thorsten-l/ESP8266-WiFi-Doorbell-Gateway/kicad/wifidoorbell/WifiDoorBell-D1-mini-B.Cu.pdf

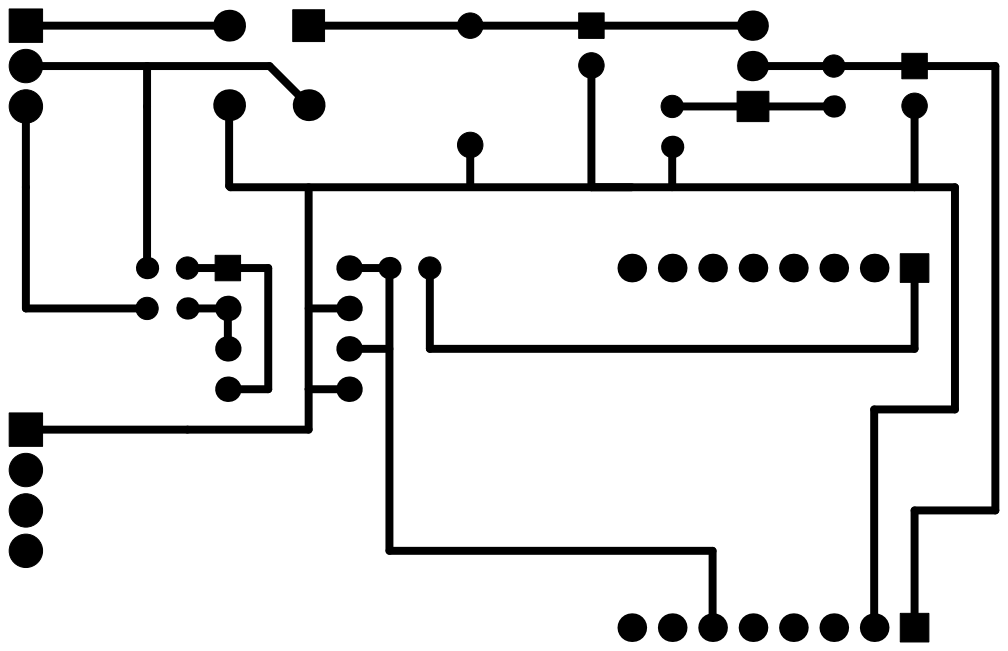
[picture p16: page 1]
