thorsten-l/ESP8266-WiFi-Doorbell-Gateway/kicad/wifidoorbell/WifiDoorBell-D1-mini-B.Mask.pdf

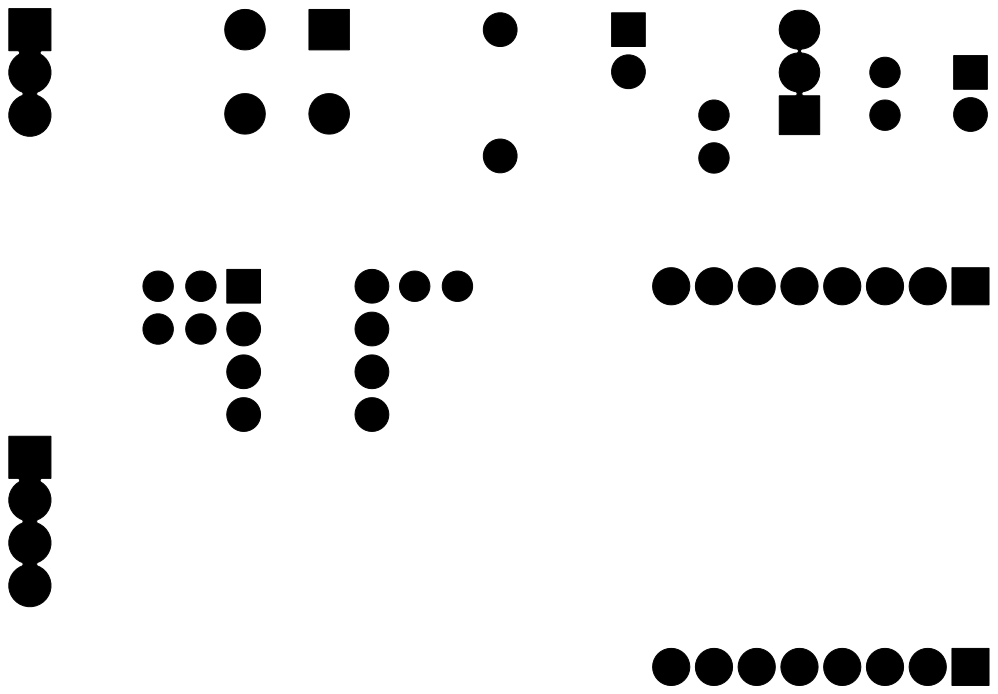
[picture p17: page 1]
