thorsten-l/ESP8266-WiFi-Doorbell-Gateway/kicad/wifidoorbell/WifiDoorBell-D1-mini-F.CrtYd.pdf

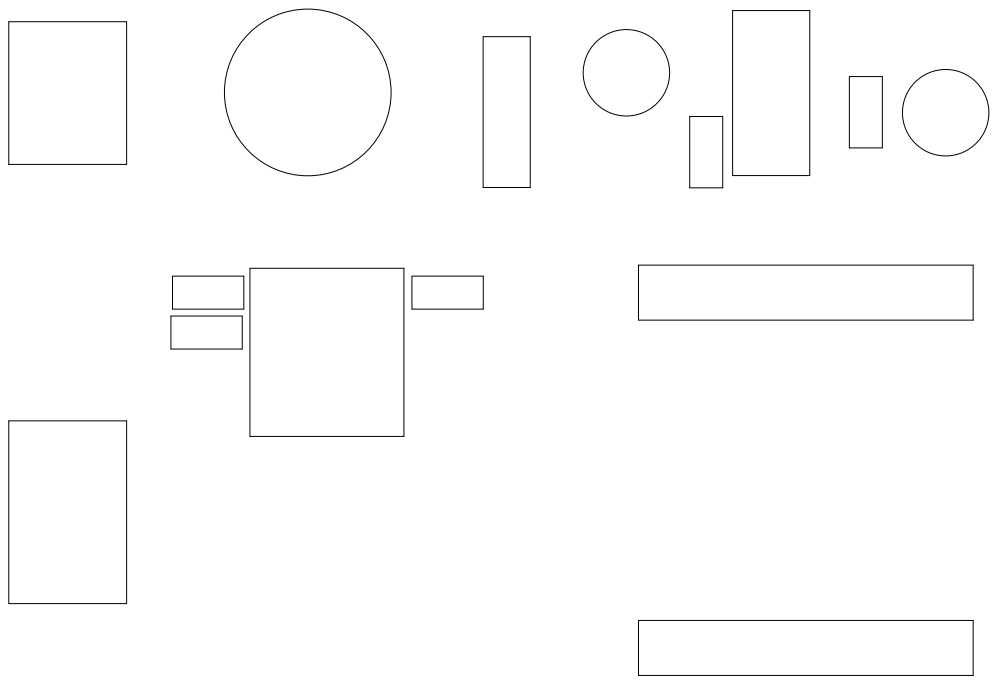
[picture p18: page 1]
