thorsten-l/ESP8266-WiFi-Doorbell-Gateway/kicad/wifidoorbell/WifiDoorBell-D1-mini-F.Cu.pdf

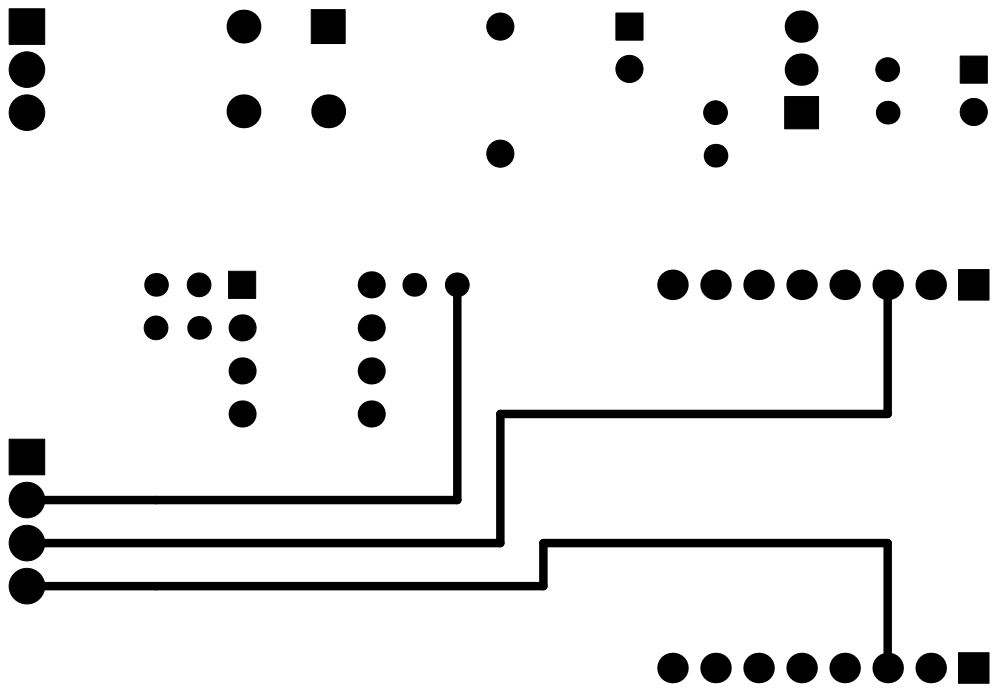
[picture p19: page 1]
