thorsten-l/ESP8266-WiFi-Doorbell-Gateway/kicad/wifidoorbell/WifiDoorBell-D1-mini-F.SilkS.pdf

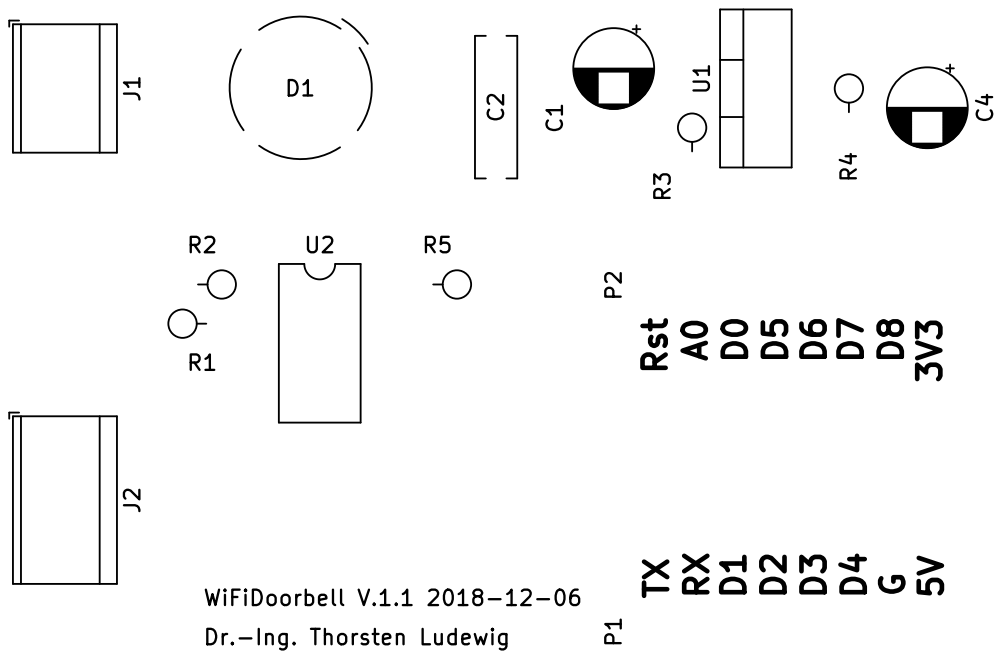
[picture p20: page 1]
