thorsten-l/ESP8266-WiFi-Doorbell-Gateway/kicad/wifidoorbell/WifiDoorBell-D1-mini.pdf

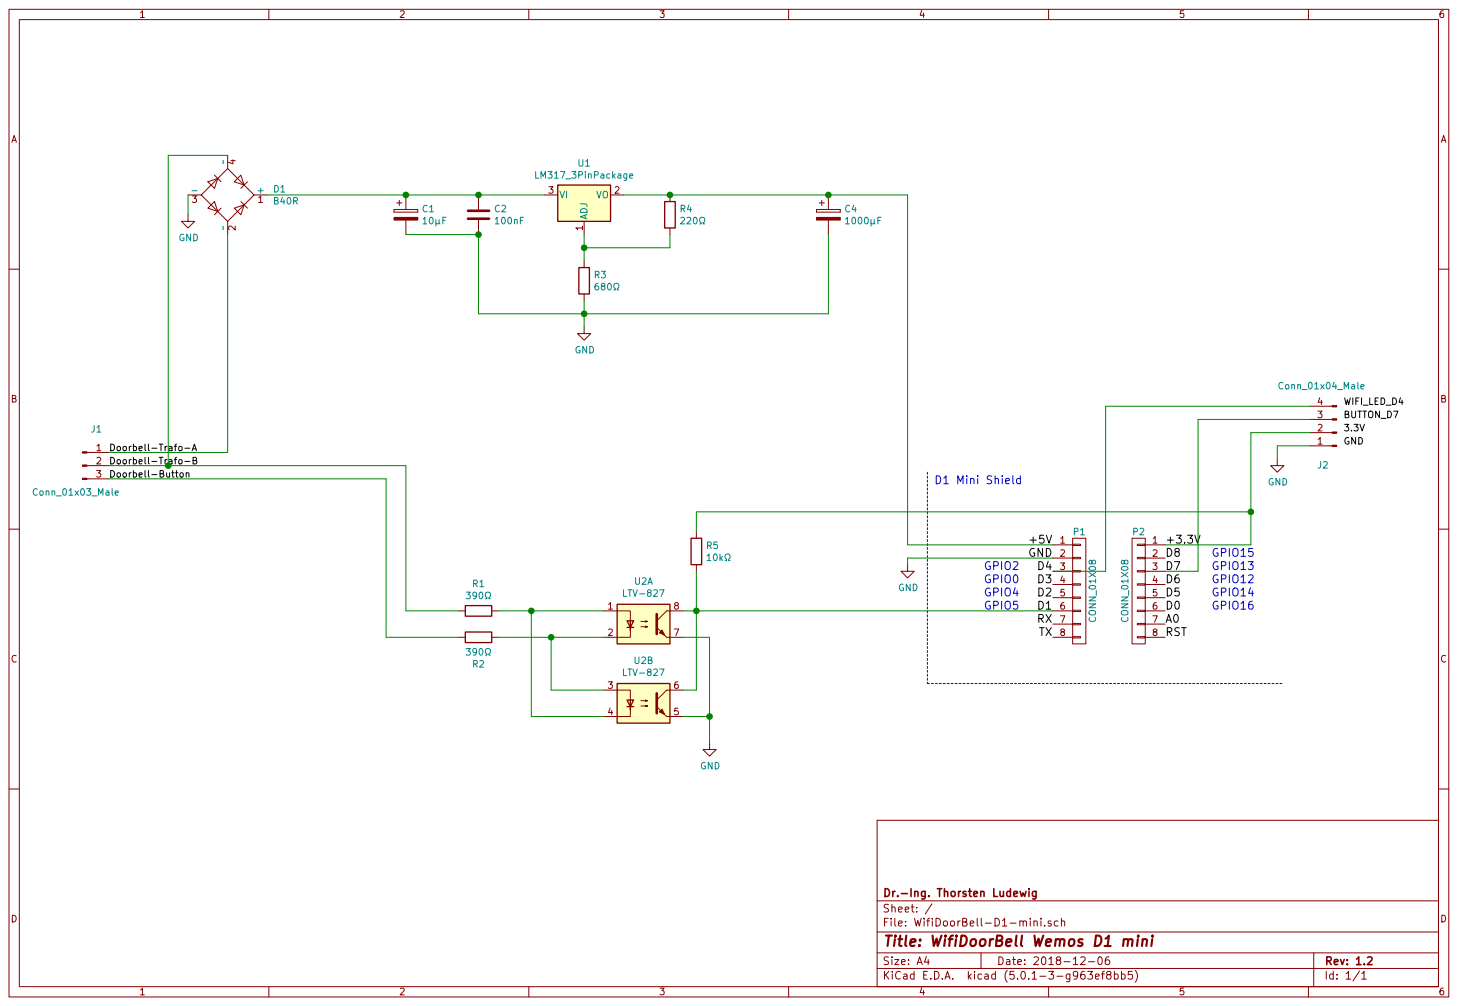
[picture p21: page 1]

Id: 1/1 Title: WifiDoorBell Wemos D1 mini File: WifiDoorBell-D1-mini.sch Sheet: / Dr.-Ing. Thorsten Ludewig
